iMike78/home-mini-v1-drop-in-pcb/[Originals]/MiciMike_silkscreen.png

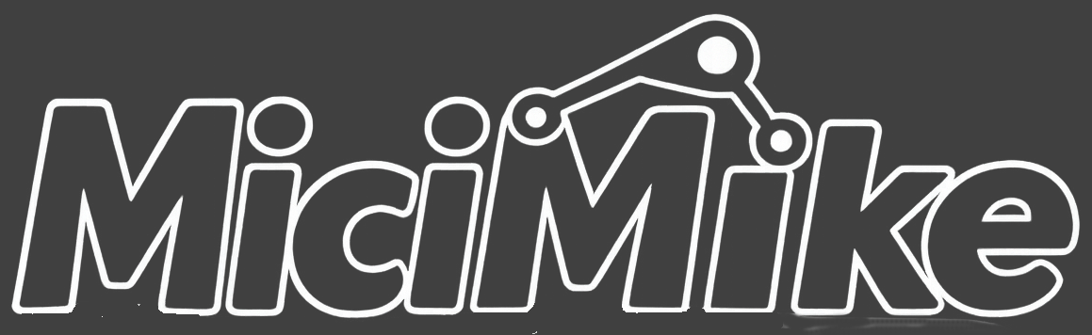
[Originals]/MiciMike_silkscreen.png
