iMike78/home-mini-v1-drop-in-pcb/pics/3D_top.png

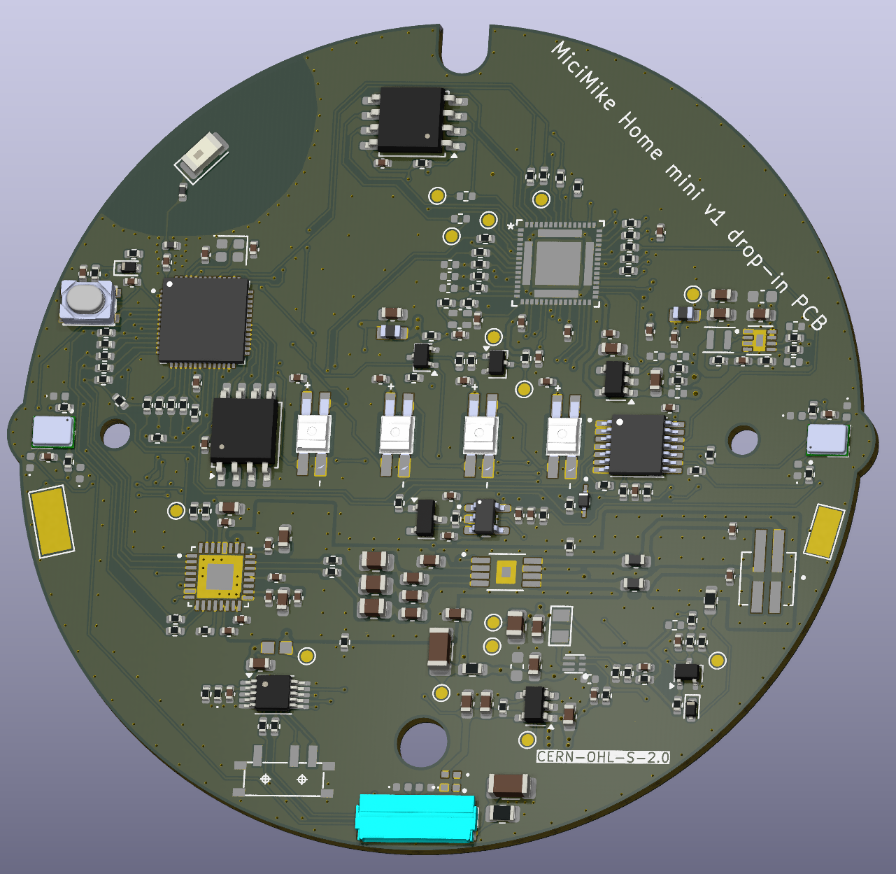
pics/3D_top.png
