iMike78/home-mini-v1-drop-in-pcb/pics/[Originals]/FPC_pinout.jpg

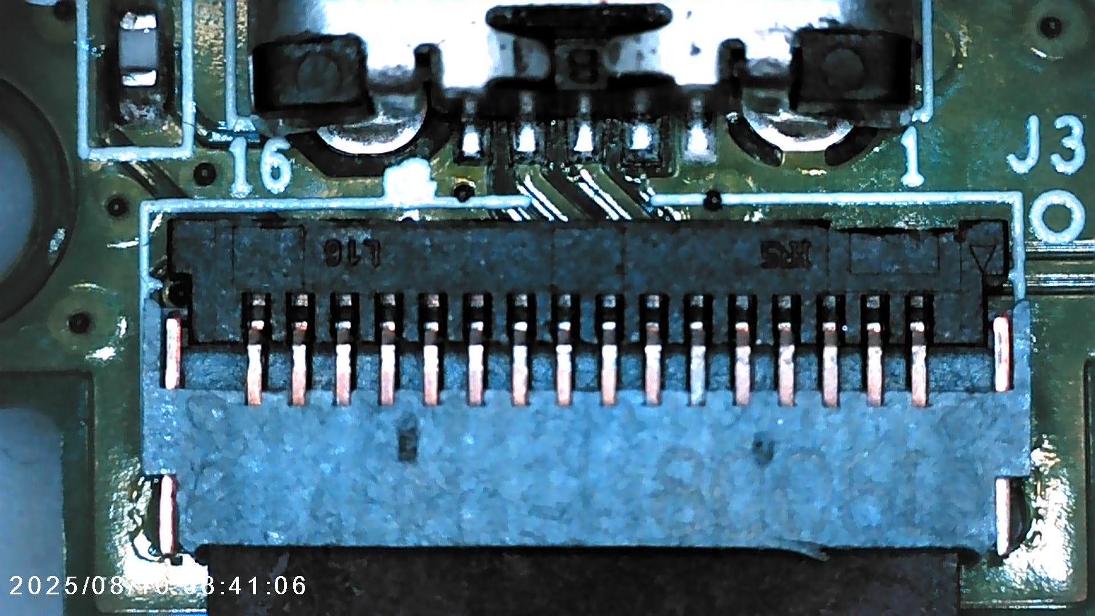
pics/[Originals]/FPC_pinout.jpg
