iMike78/home-mini-v1-drop-in-pcb/pics/DJI_20260208_104004_14.jpg

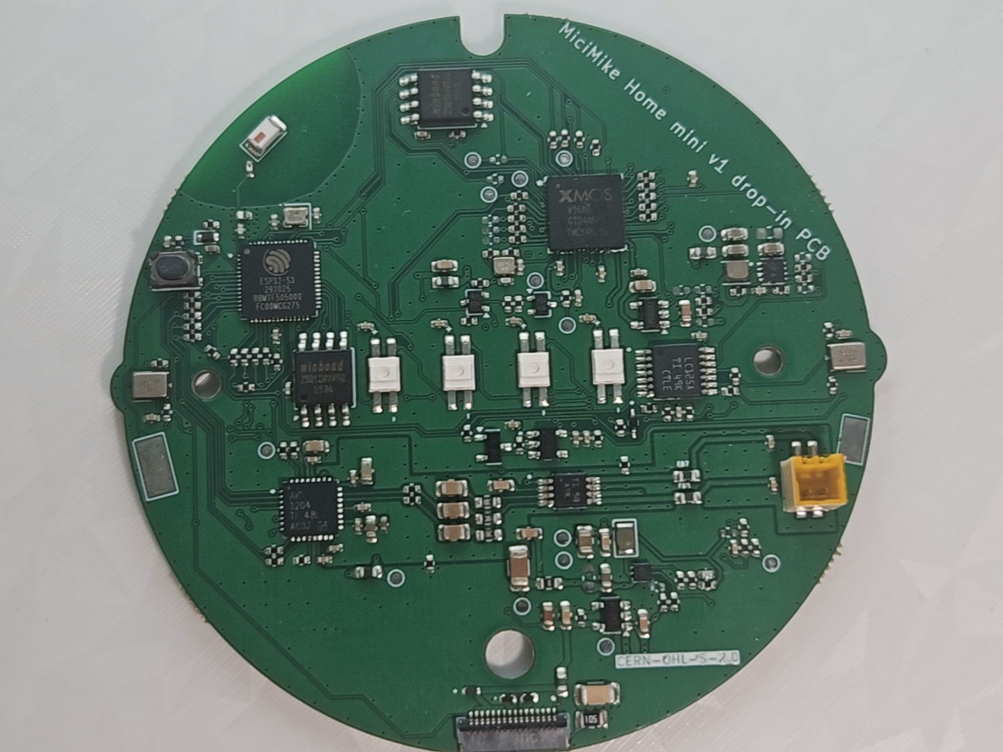
pics/DJI_20260208_104004_14.jpg
