iMike78/home-mini-v1-drop-in-pcb/pics/F_Cu.png

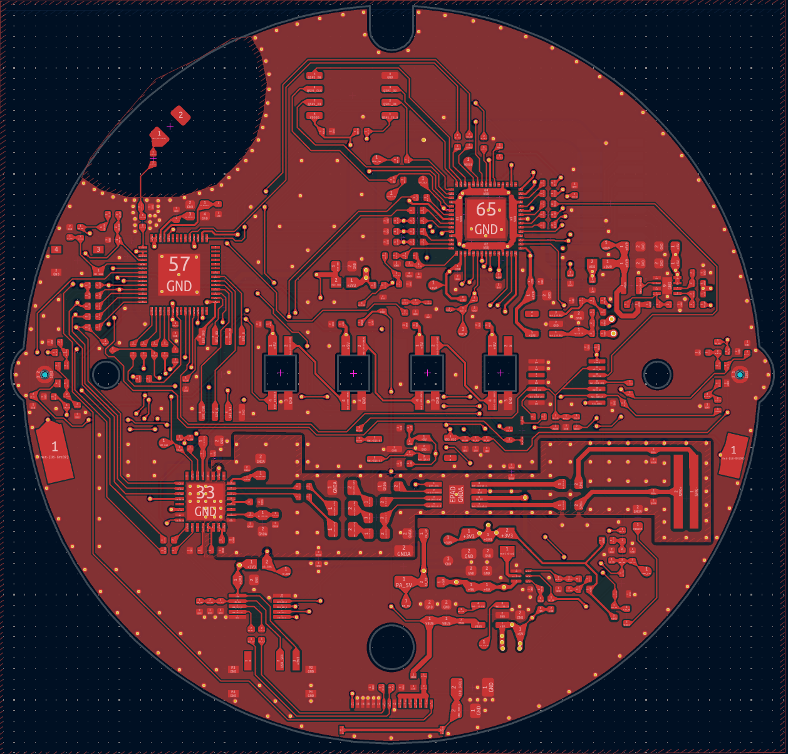
pics/F_Cu.png
