iMike78/home-mini-v1-drop-in-pcb/pics/home-mini-DiP-Gen1-front.png

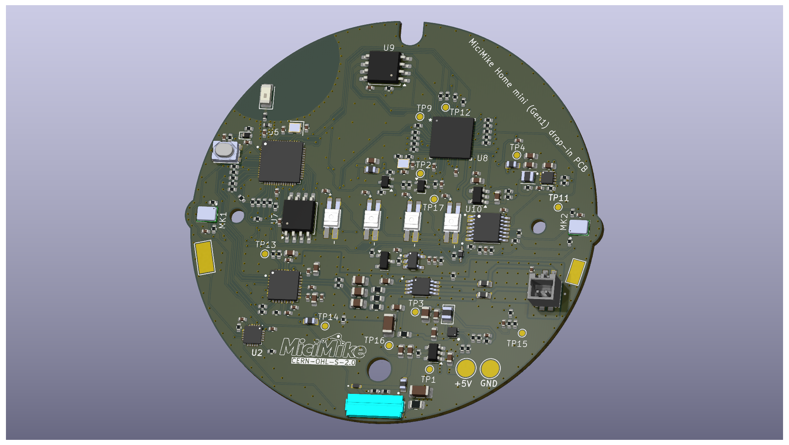
pics/home-mini-DiP-Gen1-front.png
