iMike78/home-mini-v1-drop-in-pcb/pics/In1_Cu.png

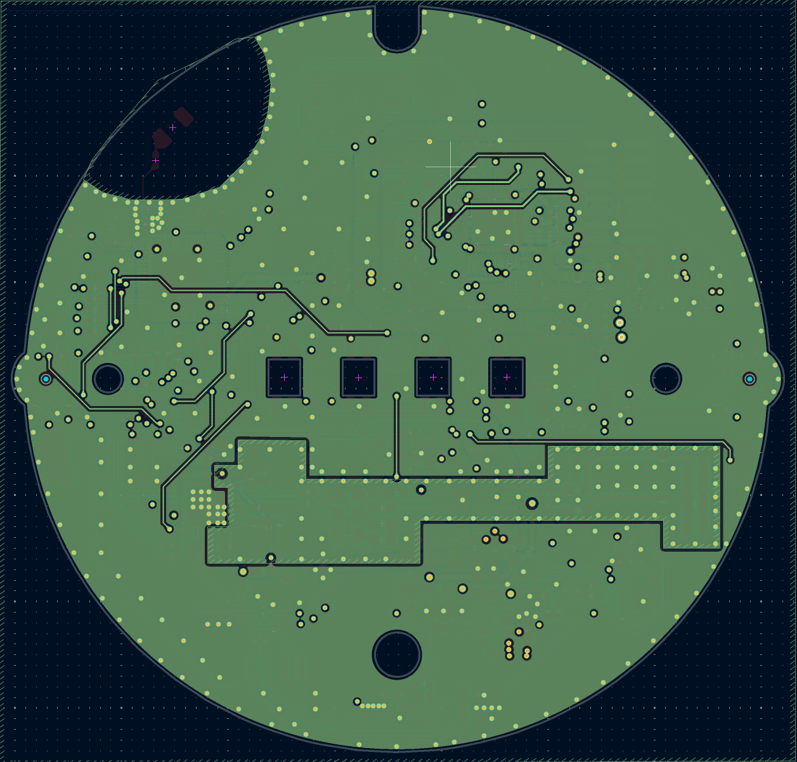
pics/In1_Cu.png
