iMike78/home-mini-v1-drop-in-pcb/pics/In2_Cu.png

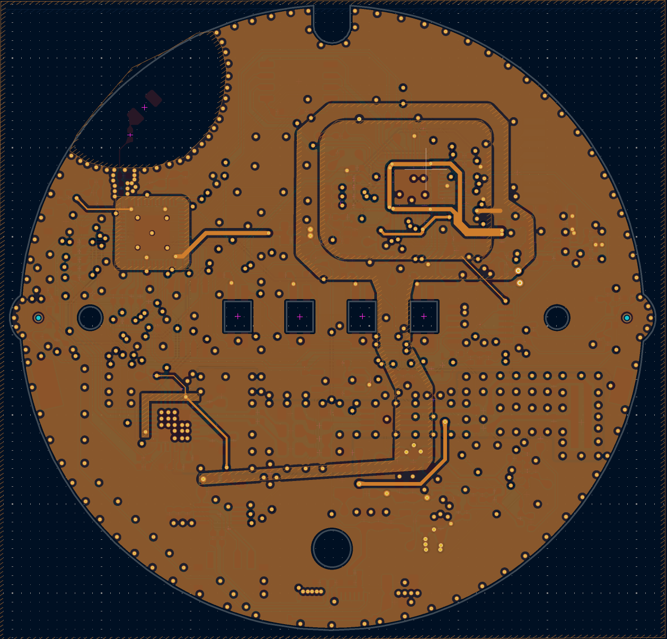
pics/In2_Cu.png
