iMike78/home-mini-v1-drop-in-pcb/pics/layout.png

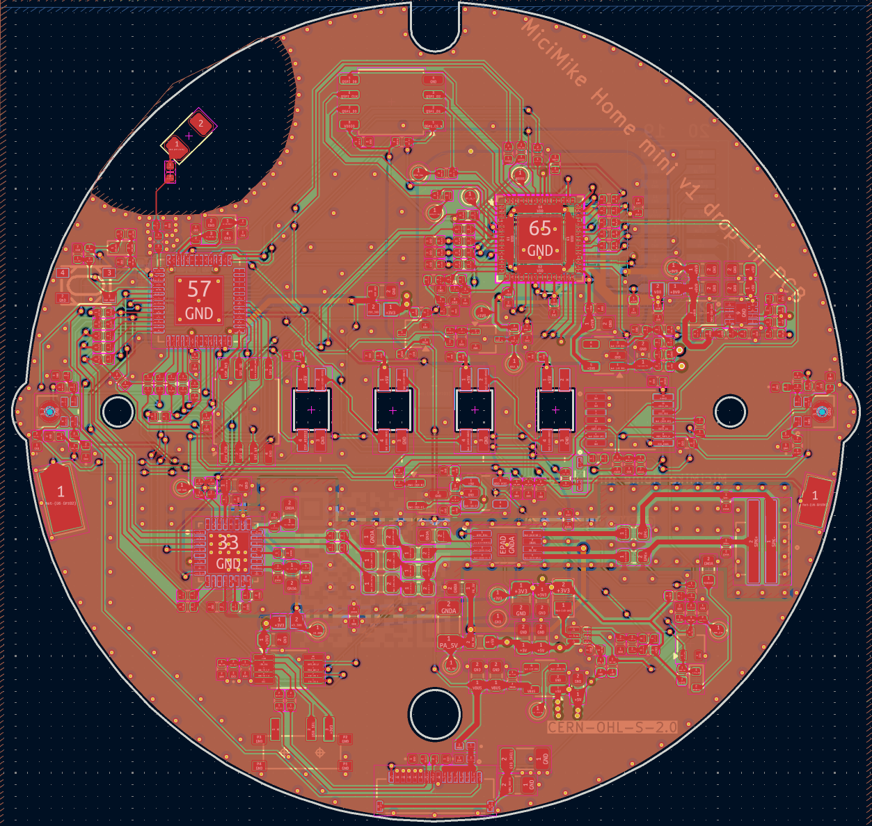
pics/layout.png
