iMike78/home-mini-v1-drop-in-pcb/pics/MiciMike_Home_Mini_v1_PCB_Prototype_1.png

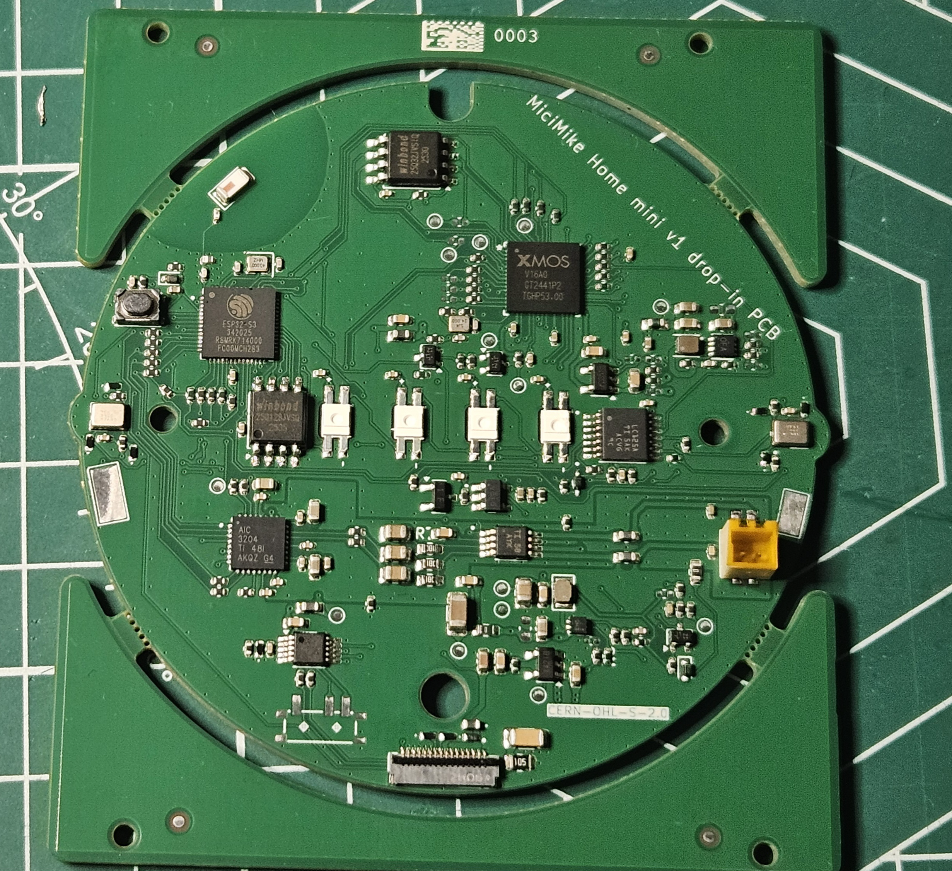
pics/MiciMike_Home_Mini_v1_PCB_Prototype_1.png
