iMike78/home-mini-v1-drop-in-pcb/pics/MiciMike_silkscreen.png

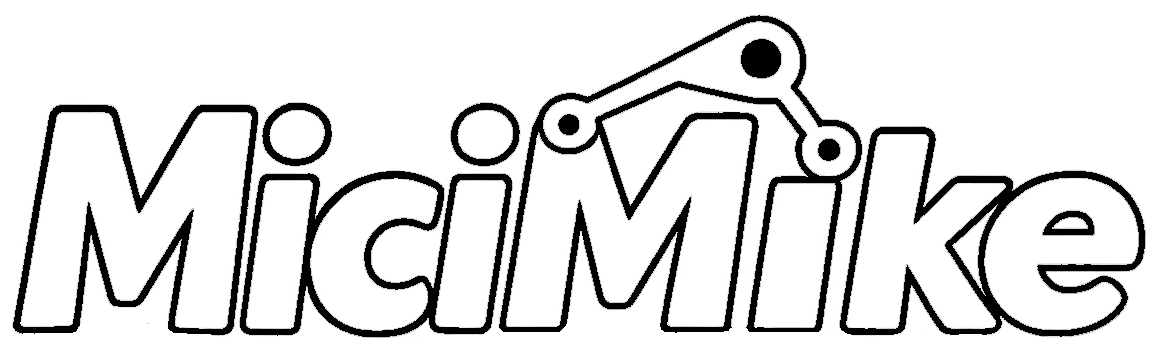
pics/MiciMike_silkscreen.png
