iMike78/home-mini-v1-drop-in-pcb/pics/Original FPC.png

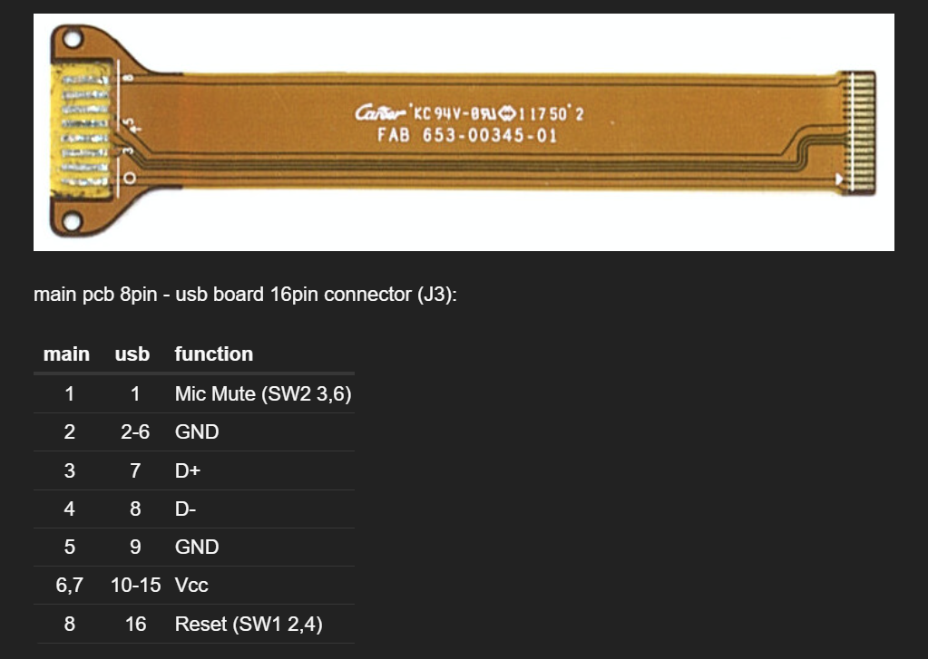
pics/Original FPC.png
