iMike78/home-mini-v1-drop-in-pcb/parts/1775443-2.stp

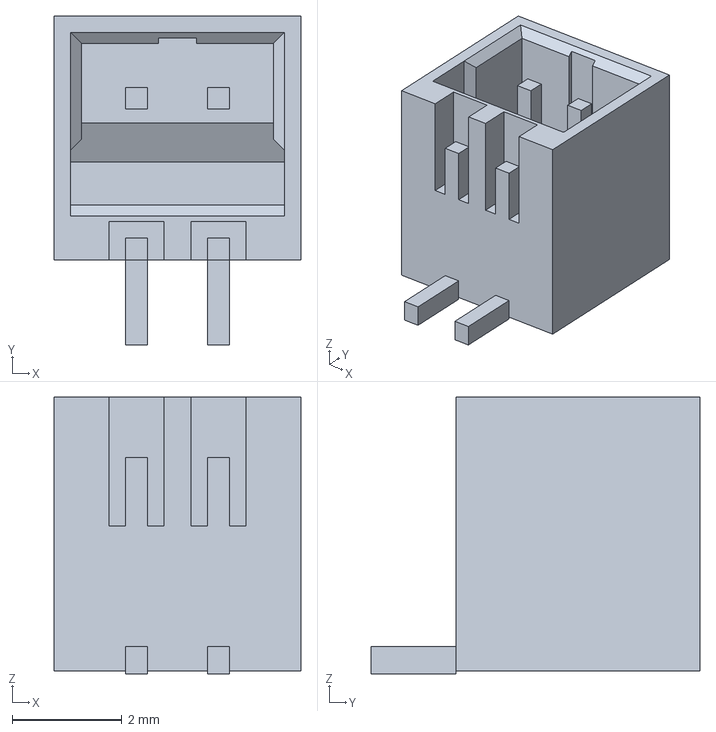
[picture p33: CAD file, 2025-08-05]
parts/1775443-2.stp
4.50 x 6.00 x 5.05 mm
