iMike78/home-mini-v1-drop-in-pcb/parts/MAX98357AETE_T.step

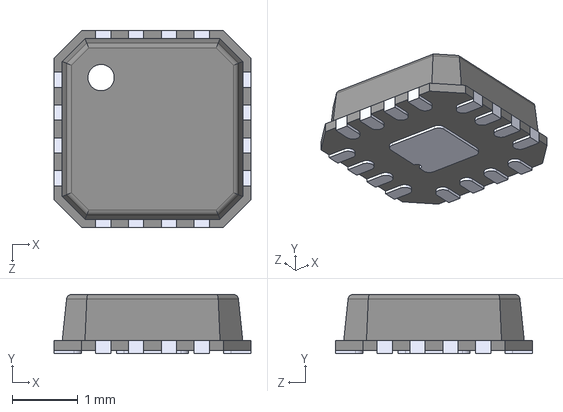
[picture p34: CAD file, 2025-08-05]
parts/MAX98357AETE_T.step
3.00 x 0.9 x 3.00 mm
